LeRobota/Akuy/readmePics/akuy25 schemas-02.png

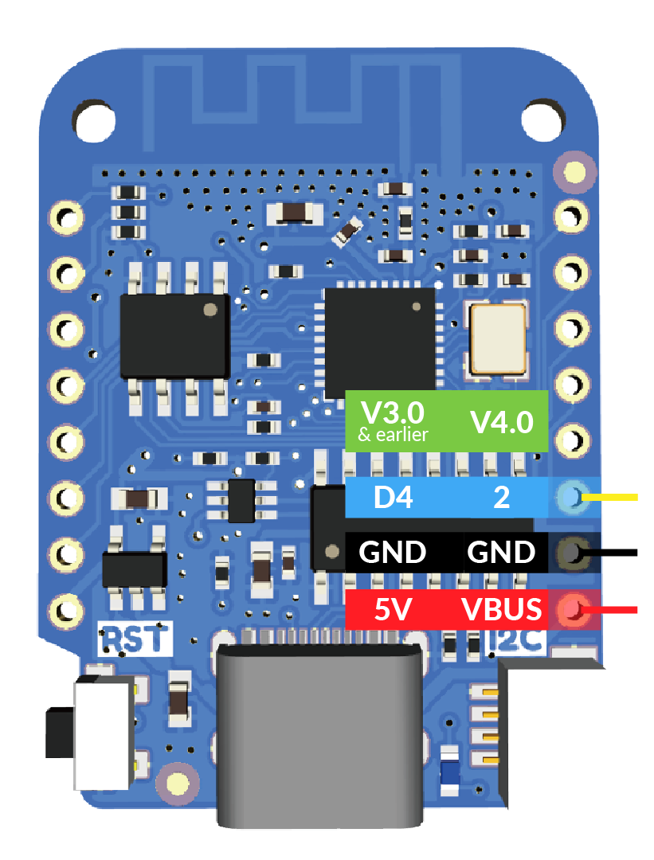
readmePics/akuy25 schemas-02.png
