LeRobota/Akuy/akuy25_blank/infos.h

// INTERNET ET CONNEXION
// Les valeurs à changer pour le wifi
const char* ssid  =    "myssid";
const char* password = "mypassword";


// VALEURS POUR LE SERVEUR WEB
 // adresse "mere" du site web
const char* host     = "api.waqi.info";
// jeton d'accès                          
const char* token   = "mytoken";
// geolocalisation actuelle 
const char* geoloc     = "myLon;myLat";                        


//luminosité led
#define lum  255
